sembre/Cable-tester-10-pair/Circuit connection/ec 10_schem.png

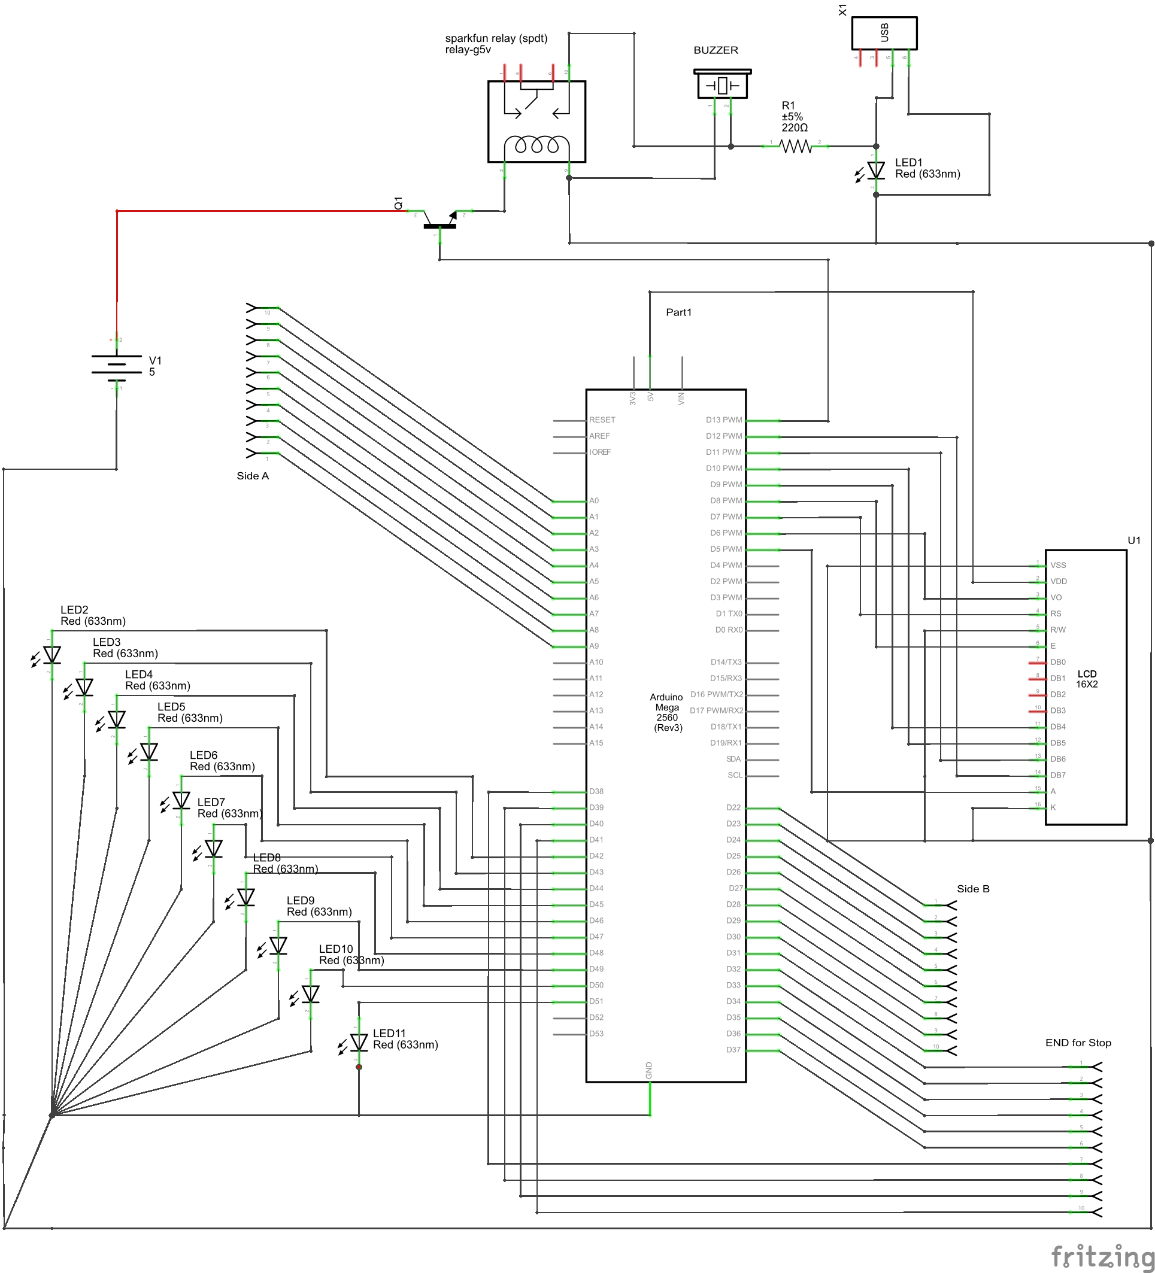
Circuit connection/ec 10_schem.png
